botanicfields/PCB-RGB-LED-276-M5Atom/BF-025/BF_DemoHueRing.cpp

// Copyright 2021 BotanicFields, Inc.
// BF-025 RGB LED Clock 276 for M5Atom
// Demonstration: HUE-ring
//   shows the FastLED Rainbow hue chart of yellow enhanced
//   to check color correction, temperature

#define FASTLED_ESP32_I2S true
//#define FASTLED_ALLOW_INTERRUPTS 0

#include <M5Atom.h>
#include "BF_RGB_LED_276.h"
#include "BF_DemoHueRing.h"

const int loop_ms = 20;          // 20ms
const int num_of_repeat = 1000;  // 20ms * 1000 = 20s

void DemoHueRing()
{
  Serial.println("[DemoHueRing]start");
  int repeat_remain = num_of_repeat;
  unsigned int last_ms = millis();

  while (repeat_remain > 0) {

    // hue rings
    for (int i = 0; i < leds1_num_of_x; ++i) {
      int hue = 256.0 * i / 60.0 + 0.5;
//      foreground_color = CHSV(hue, 255, 255);  // to check hue directly
      foreground_color = ColorFromPalette(palette_color, hue, 255);
      PutDotLeds1(i, 0);
      PutDotLeds1(i, 1);
      PutDotLeds1(i, 2);
    }

    // count down
    foreground_color = CRGB::SlateGray;
    PutInt(repeat_remain * loop_ms / 1000);

    // check button
    M5.update();
    int button_check = CheckButton();
    if (button_check == 2000 || button_check == 1000) {  // exit or go next
      Serial.println("[DemoHueRing]break");
      repeat_remain = 1;
    }
    else if (button_check != 0) {
      Serial.println("[DemoHueRing]repeat extended");
      repeat_remain = num_of_repeat;
    }

    FastLED.show();

    delay(loop_ms - (millis() - last_ms));
    --repeat_remain;
    last_ms = millis();
  }

  Serial.println("[DemoHueRing]end");
}
